andrewpeck/OH0/Footprints/STEP/LQW31HN.stp

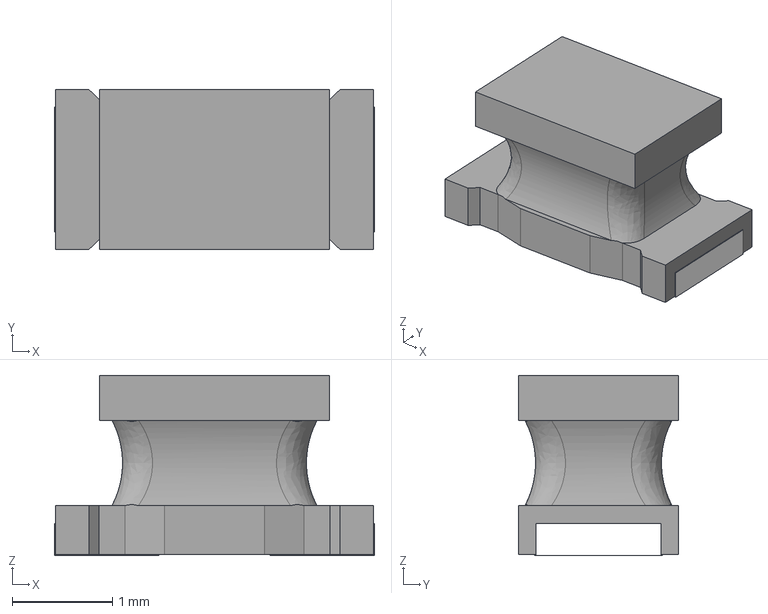
[picture p17: CAD file, 2020-09-25]
Footprints/STEP/LQW31HN.stp
3.20 x 1.60 x 1.80 mm
