andrewpeck/OH0/Footprints/STEP/LQW2BHN.stp

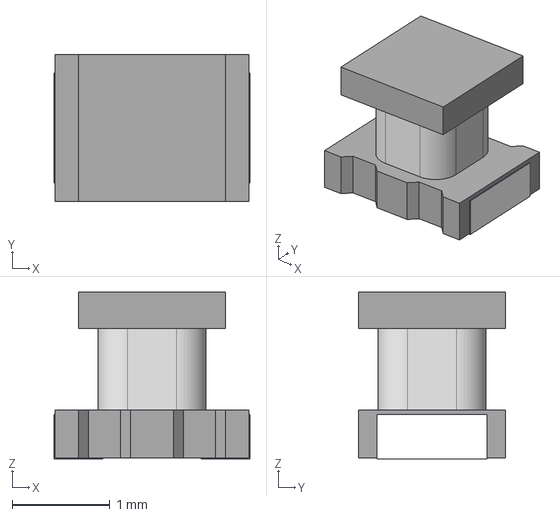
[picture p18: CAD file, 2020-09-25]
Footprints/STEP/LQW2BHN.stp
2.00 x 1.50 x 1.70 mm
