andrewpeck/OH0/Footprints/STEP/C1206.step

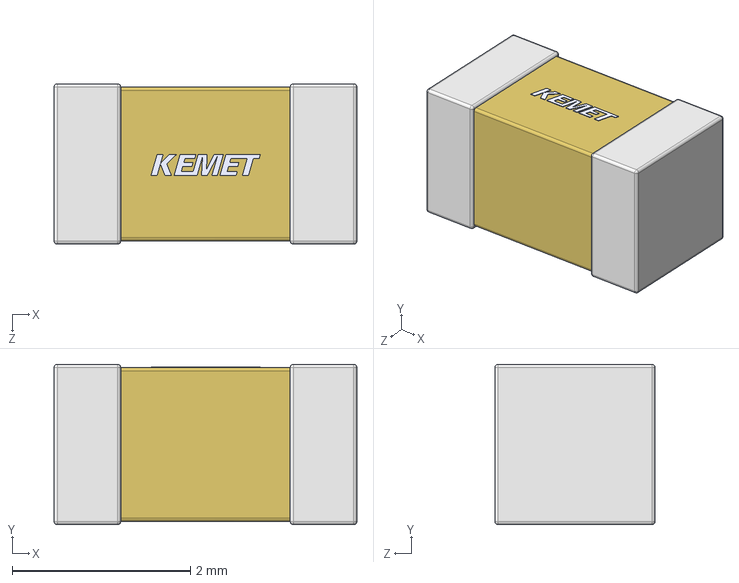
[picture p19: CAD file, 2020-09-25]
Footprints/STEP/C1206.step
3.40 x 1.80 x 1.80 mm
