andrewpeck/OH0/Footprints/STEP/Coilcraft-1812SMS-R15.STEP

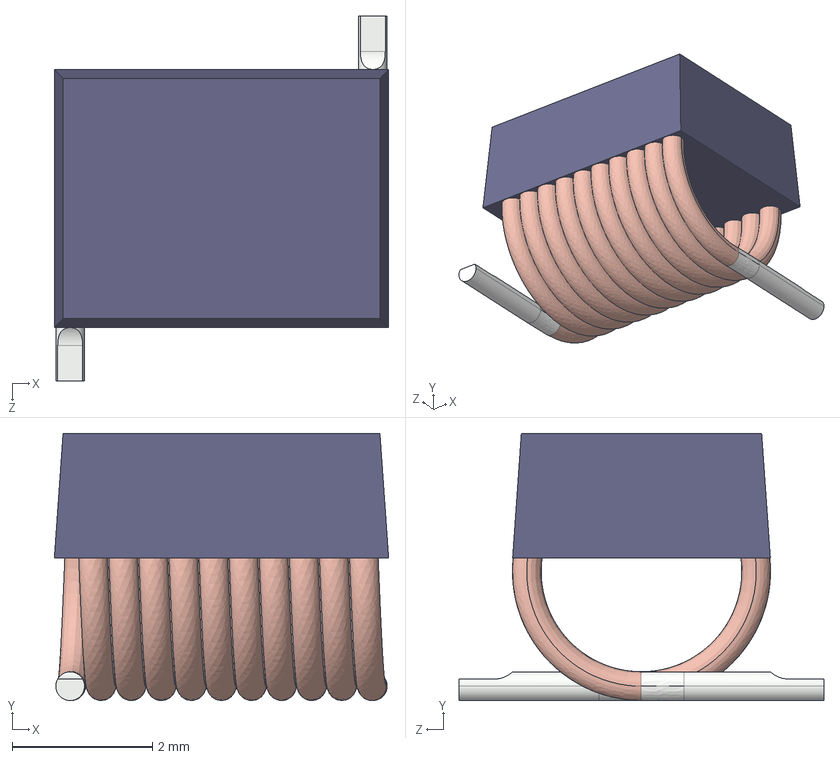
[picture p20: CAD file, 2020-09-25]
Footprints/STEP/Coilcraft-1812SMS-R15.STEP
4.77 x 3.81 x 5.21 mm
Coilcraft-1812SMS-R15_W XXATZ2-X [1812SMS]_1812SMS-R15_2
Coilcraft-1812SMS-R15_36-625 [T7-566-1]_1812SMS-XXXL_2
