andrewpeck/OH0/Footprints/STEP/SMTSO-080-2ET-PennEngineering-05-17-2018.stp

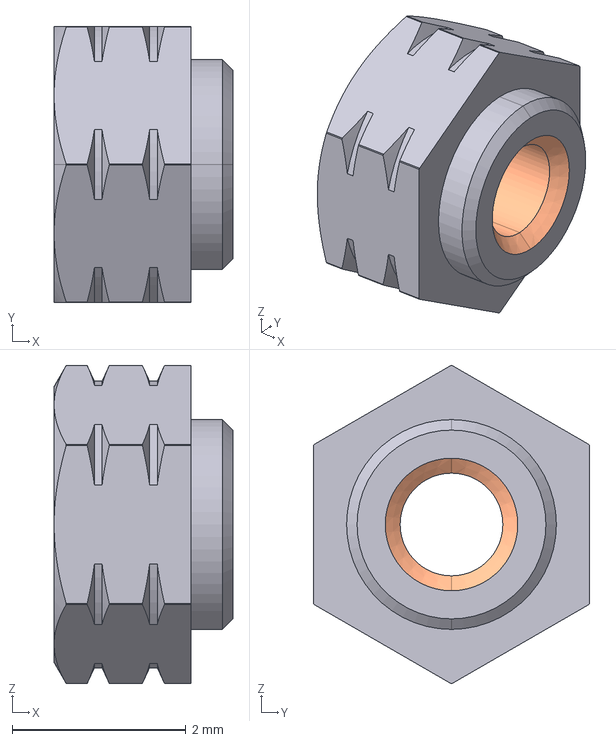
[picture p21: CAD file, 2020-09-25]
Footprints/STEP/SMTSO-080-2ET-PennEngineering-05-17-2018.stp
2.06 x 3.18 x 3.66 mm
