andrewpeck/OH0/Footprints/STEP/UDFN8_1P45X1.step

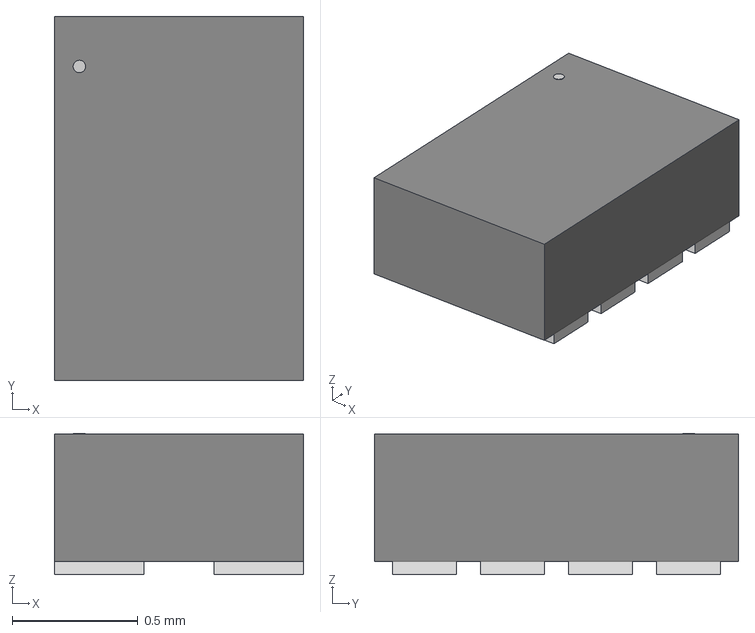
[picture p22: CAD file, 2020-09-25]
Footprints/STEP/UDFN8_1P45X1.step
0.99 x 1.45 x 0.561 mm
