andrewpeck/OH0/Footprints/STEP/LED0603.step

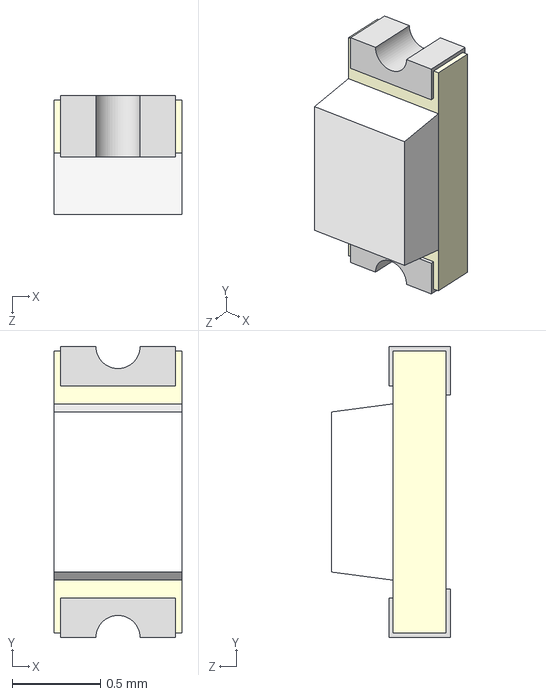
[picture p23: CAD file, 2020-09-25]
Footprints/STEP/LED0603.step
0.725 x 1.65 x 0.675 mm
