andrewpeck/OH0/Footprints/STEP/SRP2010 series.stp

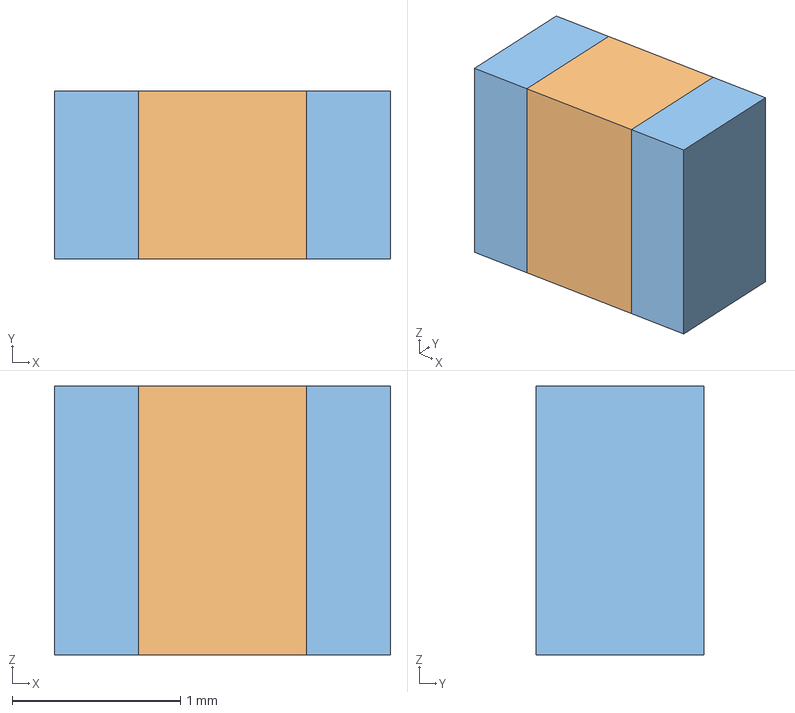
[picture p24: CAD file, 2020-09-25]
Footprints/STEP/SRP2010 series.stp
2.00 x 1.00 x 1.60 mm
A
B x 2
COPPER
