andrewpeck/OH0/Footprints/STEP/AIAC-4125C.STEP

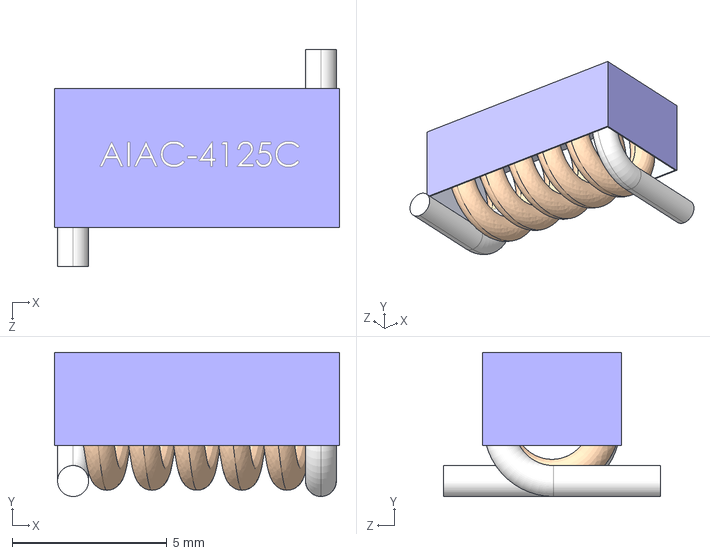
[picture p25: CAD file, 2020-09-25]
Footprints/STEP/AIAC-4125C.STEP
9.20 x 4.65 x 7.00 mm
