andrewpeck/OH0/Footprints/STEP/DRY0006A.stp

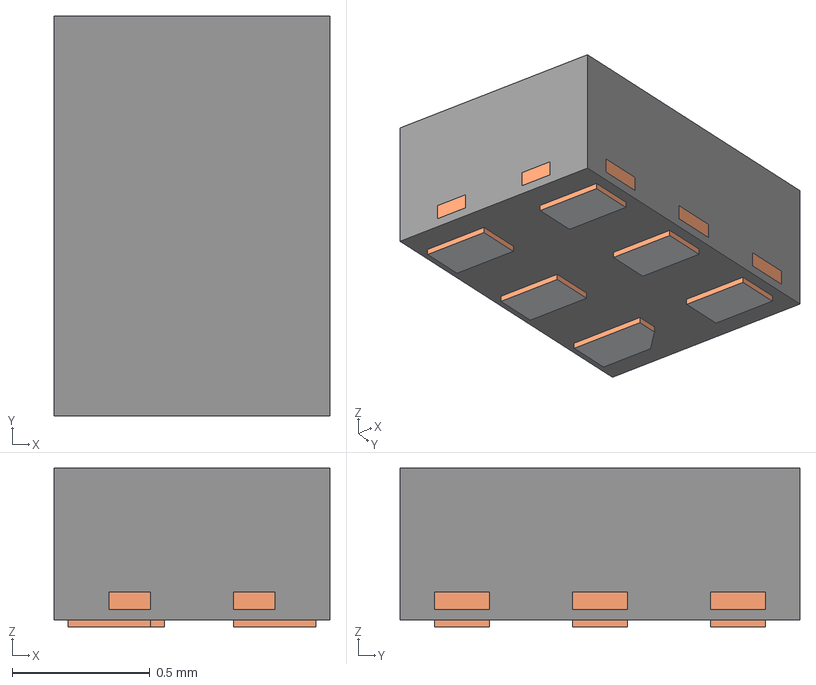
[picture p26: CAD file, 2020-09-25]
Footprints/STEP/DRY0006A.stp
1.00 x 1.45 x 0.575 mm
BODY-SON
FRAME-DRY0006A
PIN1-ID
