andrewpeck/OH0/Footprints/STEP/C0201.step

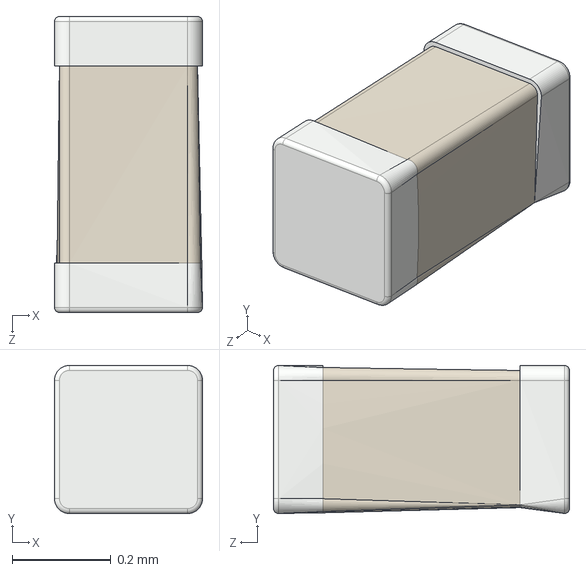
[picture p27: CAD file, 2019-04-02]
Footprints/STEP/C0201.step
0.3 x 0.3 x 0.6 mm
