andrewpeck/OH0/Footprints/STEP/DF40C-40DP.stp

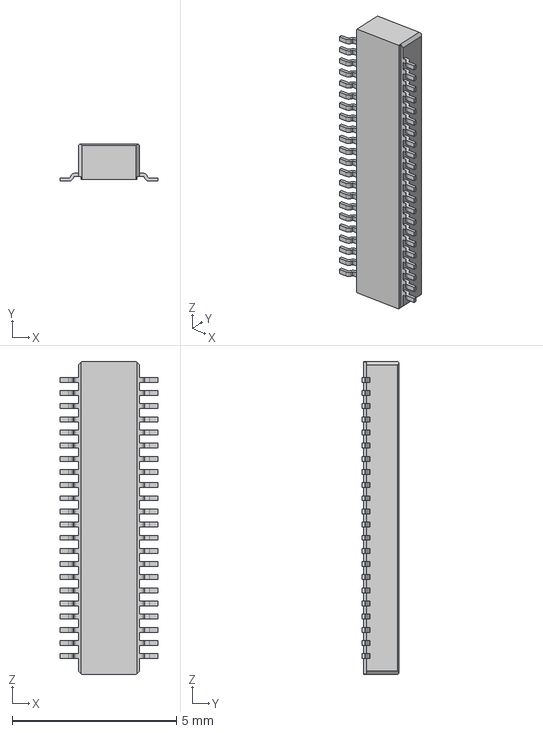
[picture p28: CAD file, 2018-12-06]
Footprints/STEP/DF40C-40DP.stp
2.97 x 1.14 x 9.52 mm
