andrewpeck/OH0/Footprints/STEP/DF40C-2P0-40DS.stp

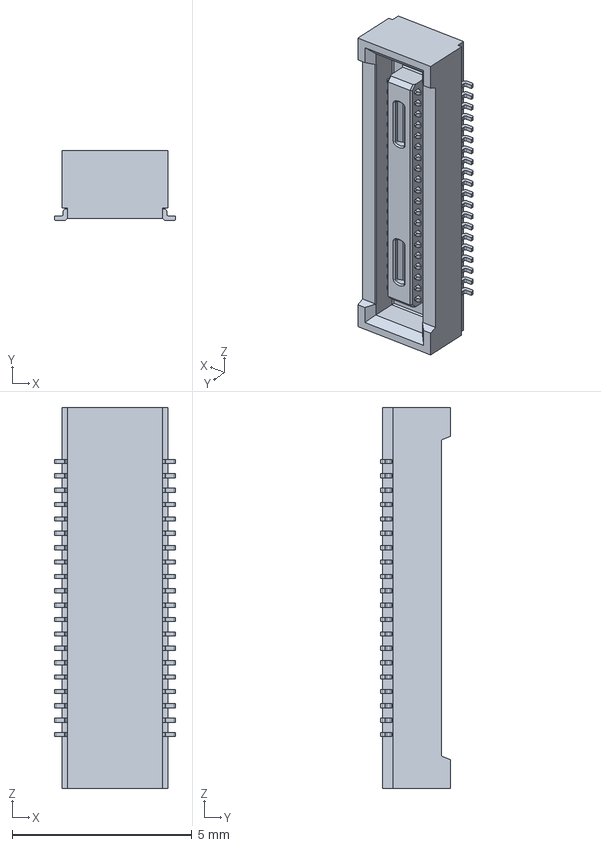
[picture p29: CAD file, 2018-12-06]
Footprints/STEP/DF40C-2P0-40DS.stp
3.38 x 1.95 x 10.6 mm
