andrewpeck/OH0/Footprints/STEP/DF40GB-48DP-0.4V.stp

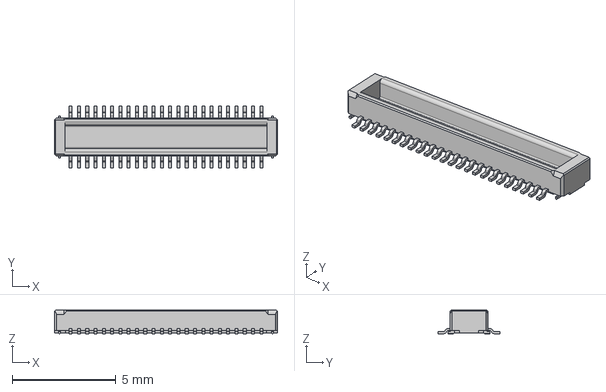
[picture p30: CAD file, 2018-12-06]
Footprints/STEP/DF40GB-48DP-0.4V.stp
10.8 x 2.97 x 1.14 mm
